alpnak/Analog_Common_Emitter_Amplifier/faz4/breadboard.jpeg

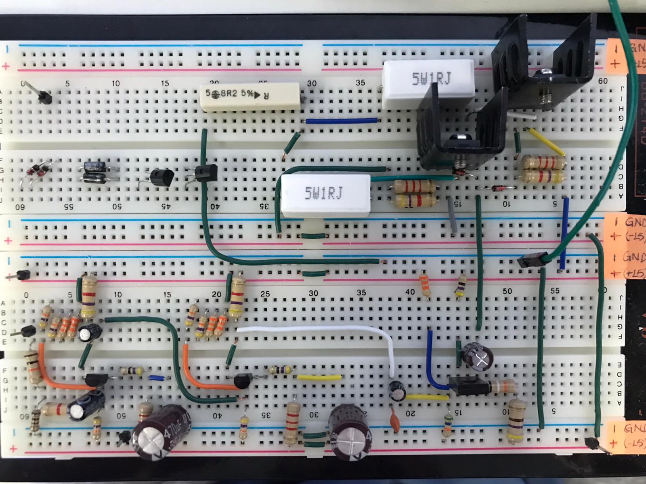
faz4/breadboard.jpeg
