alpnak/Analog_Common_Emitter_Amplifier/faz3/faz1.asc

+Vcc: voltage; 15
-Vcc: voltage; -15
C1: cap; 4.7e-6
C2: cap; 2.2e-6
CE: cap; 470e-6
CH: cap; 2e-9
R1: res; 47e3
R2: res; 160e3
RC: res; 4.7e3
RE1: res; 47
RE2: res; 2.2e3
RL: res; 20e3
T1: npn; BC546B
Vin: voltage; ""
Named nets: 0, Vout
