alpnak/Analog_Common_Emitter_Amplifier/faz3/faz2A.asc

+Vcc: voltage; 15
-Vcc: voltage; -15
C1: cap; 1e-6
C2: cap; 22e-6
R1: res; 56e3
R2: res; 33e3
RC: res; 47
RE: res; 510
RL: res; 1.3e3
RS: res; 4.7e3
T1: npn; BD139-16
Vin: voltage; ""
Named nets: 0, Vout
.model BD139-16 NPN(IS=2.37E-13 VAF=93.6 BF=200 IKF=1.23 NE=1.45 ISE=2.1E-13 IKR=0.05 ISC=1.5E-13 NC=1.65 BR=10 RC=0.17 CJC=5.5E-11 MJC=0.31 VJC=0.35 CJE=1.1E-10 TF=1.2E-9 TR=1.5E-8 Vceo=80 Icrating=1.5 mfg=Philips)
