alpnak/Analog_Common_Emitter_Amplifier/faz3/faz2B.asc

+Vcc: voltage; 15
-Vcc: voltage; -15
CC1: cap; 4.7e-6
CC2: cap; 2.2e-6
CC3: cap; 2.2e-6
CC4: cap; 22e-6
CE1: cap; 470e-6
CE2: cap; 470e-6
CH: cap; 2e-9
R1.1: res; 47e3
R1.2: res; 47e3
R1.3: res; 56e3
R2.1: res; 160e3
R2.2: res; 160e3
R2.3: res; 33e3
RC1: res; 4.7e3
RC2: res; 4.7e3
RC3: res; 47
RE1.1: res; 47
RE1.2: res; 47
RE2.1: res; 2.2e3
RE2.2: res; 2.2e3
RE: res; 510
RL: res; 1.3e3
RS: res; 4.7e3
T1: npn; BC546B
T2: npn; BC546B
T3: npn; BD139-16
Vin: voltage; ""
Named nets: 0, Vout
.model BD139-16 NPN(IS=2.37E-13 VAF=93.6 BF=200 IKF=1.23 NE=1.45 ISE=2.1E-13 IKR=0.05 ISC=1.5E-13 NC=1.65 BR=10 RC=0.17 CJC=5.5E-11 MJC=0.31 VJC=0.35 CJE=1.1E-10 TF=1.2E-9 TR=1.5E-8 Vceo=80 Icrating=1.5 mfg=Philips)
