alpnak/Analog_Common_Emitter_Amplifier/faz3/faz3.asc

+Vcc: voltage; 15
-Vcc: voltage; -15
C1: cap; 100e-6
D3: diode; 1N4148
D4: diode; 1N4148
R1: res; 1.5e3
R2: res; 1.5e3
RE1: res; 1
RE2: res; 1
RL: res; 8
RS: res; 21
T1: pnp; BD140
T2: npn; BD139
Vin: voltage; ""
Named nets: 0, Vout
.model BD139 NPN(IS=1E-13 BF=160 VAF=100 IKF=1.5 ISE=1E-14 NE=1.5 RE=0.1 RC=0.1 RB=1 CJE=100p VJE=0.7 MJE=0.33 CJC=50p VJC=0.55 MJC=0.33 TF=1n TR=10n Vceo=80 Icrating=1.5 mfg=ST)
.model BD140 PNP(IS=1E-13 BF=160 VAF=100 IKF=1.5 ISE=1E-14 NE=1.5 RE=0.1 RC=0.1 RB=1 CJE=100p VJE=0.7 MJE=0.33 CJC=50p VJC=0.55 MJC=0.33 TF=1n TR=10n Vceo=80 Icrating=1.5 mfg=ST)
