alpnak/Analog_Common_Emitter_Amplifier/faz2/faz2A.asc

+Vcc: voltage; 15
-Vcc: voltage; -15
C1: cap; 1e-6
C2: cap; 22e-6
R1: res; 56e3
R2: res; 33e3
RC: res; 47
RE: res; 510
RL: res; 1.3e3
RS: res; 4.7e3
T1: npn; BJT
Vin: voltage; ""
Named nets: 0, Vout
.model BJT NPN(IS=1e-14 BF=180)
