alpnak/Analog_Common_Emitter_Amplifier/faz2/faz2A_DC_eqv.asc

+Vcc: voltage; 15
-Vcc: voltage; -15
R1: res; 27e3
R2: res; 22e3
RC: res; 220
RE: res; 1.5e3
T1: npn; BJT
Named nets: 0
.model BJT NPN(BF=180)
