alpnak/Analog_Common_Emitter_Amplifier/faz2/faz2B.asc

+Vcc: voltage; 15
-Vcc: voltage; -15
CC1: cap; 4.7e-6
CC2: cap; 2.2e-6
CC3: cap; 2.2e-6
CC4: cap; 22e-6
CE1: cap; 470e-6
CE2: cap; 470e-6
CH: cap; 2e-9
R1.1: res; 47e3
R1.2: res; 47e3
R1.3: res; 56e3
R2.1: res; 160e3
R2.2: res; 160e3
R2.3: res; 33e3
RC1: res; 4.7e3
RC2: res; 4.7e3
RC3: res; 47
RE1.1: res; 100
RE1.2: res; 100
RE2.1: res; 2.2e3
RE2.2: res; 2.2e3
RE: res; 510
RL: res; 1.3e3
RS: res; 4.7e3
T1: npn; BJT1
T2: npn; BJT2
T3: npn; BJT3
Vin: voltage; ""
Named nets: 0, Vout
.model BJT3 NPN(IS=1e-14 BF=180)
.model BJT1 NPN(IS=1e-14 BF=180 CJE=0 CJC=0)
.model BJT2 NPN(IS=1e-14 BF=180 CJE=0 CJC=0)
