alpnak/Analog_Common_Emitter_Amplifier/faz1/faz1_DC_eqv.asc

+Vcc: voltage; 15 V
-Vcc: voltage; -15 V
R1: res; ""
R2: res; ""
RC: res; ""
RE1: res; ""
RE2: res; ""
T1: npn; BJT
Named nets: 0
.model BJT NPN(BF=180 CJE=0 CJC=0)
